zhushengji/3.12OLED_Smooth_animated_smart_alarm-clock/Beautiful_Clock/src/gb2312.c

/*
  Fontname: -WenQuanYi-WenQuanYi Bitmap Song-Medium-R-Normal--14-100-100-100-P-138-ISO10646--1
  Copyright: (null)
  Glyphs: 7679/22949
  BBX Build Mode: 0
*/
#include <clib/u8g2.h>
#ifdef U8G2_USE_LARGE_FONTS
const uint8_t dinkie_9[52247] U8G2_FONT_SECTION("dinkie_9") = 
  "\17\0\3\3\4\4\3\3\5\13\12\376\376\7\376\7\376\0\304\1\350\2\361 \5\0\344\4!\7q\345"
  "D%\0$\20\225\234Ul\222\42\211\315\42\222\224Y\10\0&\16u\244\215(%-$\211\210\42\223"
  "\0,\7\62\324LD\2.\6\21\244D\0\60\12td\215$\244SD\2\61\7r\344\314$\17\62"
  "\12td\215$\24\13e#\63\15td\215$\24\213\10E\21\11\0\64\17ud\225(\22\212$E"
  "B\221Z\4\0\65\13tdEm\30\23E$\0\66\14td\215$\66\11)E$\0\67\13td"
  "\5-\24\13\305\222\0\70\16td\215$$\212HB\242\210\4\0\71\15td\215$$\212\314D\21"
  "\11\0\77\14td\215$\24\13\245\3B\0@\15v\344\325(&\242\204$\223p\1A\14u\244U"
  ",\22\212\244\335d\1B\14td\305$$\242\204D\24\0C\13u\244\315$&\314\26\231\0D\12"
  "u\244\5%\246Sd\4E\12tdE-\66\211\305\10F\12tdE-\66\211\245\1G\14u\244"
  "\315$&\214\320d\21\2H\11u\244EL\355\246\26I\11s$\305$\224\313\0J\12td]n"
  "\242\210\4\0K\14tdEH%\42\212$\211\2L\10tdE,o\4M\17v\344Ep&\211"
  "L\42\243\210(\42\14N\14u\244El$\211\210fj\1O\12u\244\315$\246[d\2P\13t"
  "d\305$$\242\304\322\0Q\14u\244\315$\246F\21\205$\1R\13td\305$$\242d\22\5S"
  "\12td\15\61Q\24\221\0T\11u\244E)\230'\0U\12u\244ELo\221\11\0V\15ud"
  "EL-\222\24\211\5C\0W\24xdFX\26\212\204\42\241HD\24\211\310\342\200(\0X\14u"
  "dEL\26IKI\223\5Y\13udEL\26I\13f\2Z\13td\5)\26\212\205b\4a"
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
  "\211\10M\21I\210\22\14E*\42QD\1\214\1\26\230\134NH\30I\265HB!J(\22\12Q"
  "$I!\2\214\3\23\230\134N\244\244v\11I\42\225\224I\276L\204\1\214\10\31\230\134N(\42\212"
  "\244\3\42\222I: \24\221\204\42!Y(\62\11\214\12\24\230\134N,Z\213\215F\241QJ(\64"
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
